Robotics-and-AI/collaborative-tasks-benchmark/stl_files/Snap/Building_Snap_Top.stl

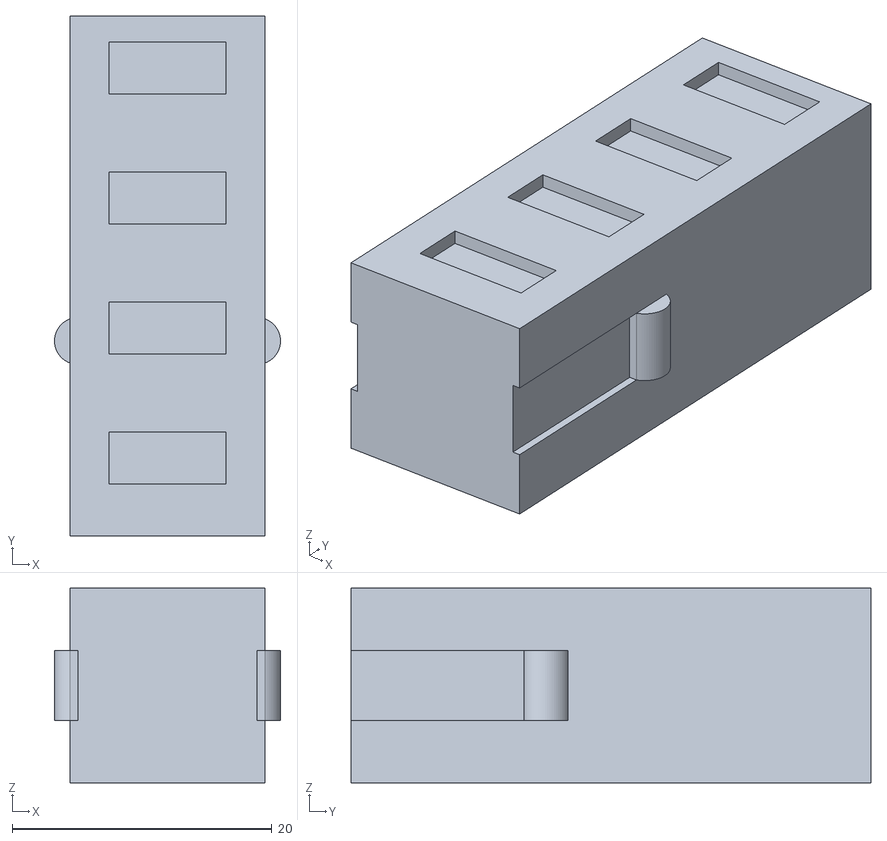
[picture p21: CAD file, 2023-07-17]
stl_files/Snap/Building_Snap_Top.stl
17.4 x 40.0 x 15.0
