Robotics-and-AI/collaborative-tasks-benchmark/stl_files/Wheel/Wheel_Base.stl

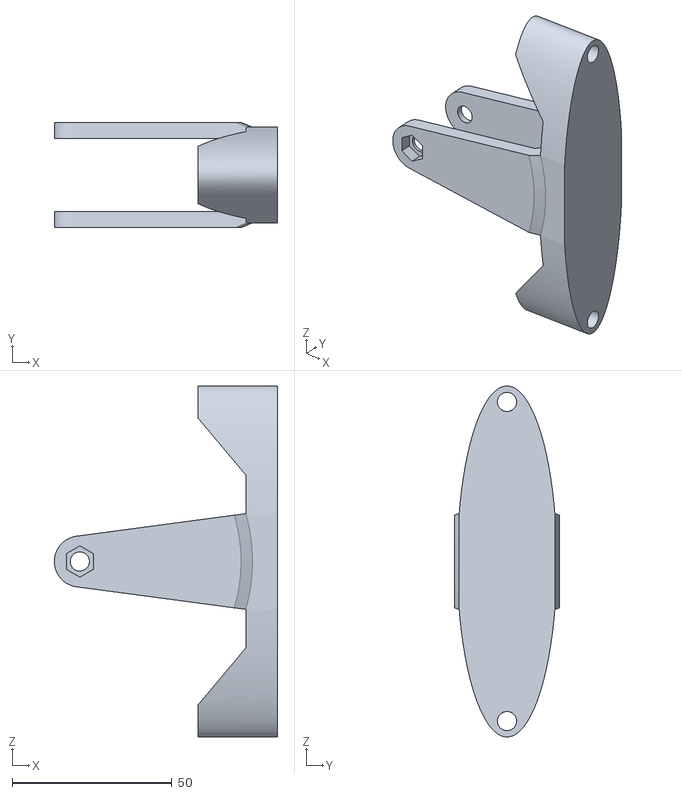
[picture p22: CAD file, 2023-09-15]
stl_files/Wheel/Wheel_Base.stl
70.0 x 33.0 x 110.0
