Robotics-and-AI/collaborative-tasks-benchmark/stl_files/Bridge/Bridge_Roof.stl

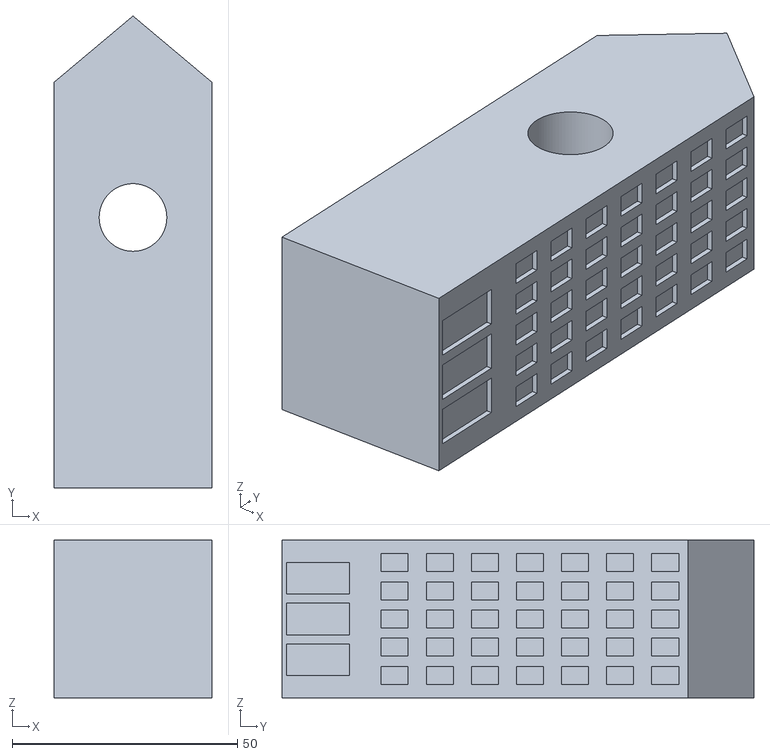
[picture p23: CAD file, 2023-07-07]
stl_files/Bridge/Bridge_Roof.stl
35.0 x 104.7 x 35.0
