Robotics-and-AI/collaborative-tasks-benchmark/stl_files/Hospital/Hospital_Top.stl

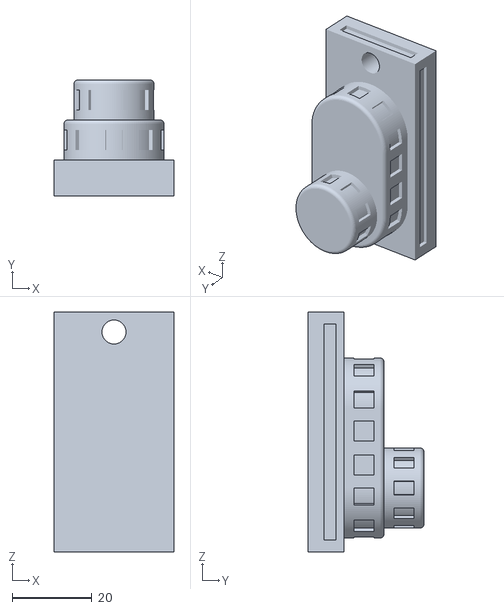
[picture p24: CAD file, 2023-07-07]
stl_files/Hospital/Hospital_Top.stl
30.0 x 29.0 x 60.0
