Robotics-and-AI/collaborative-tasks-benchmark/stl_files/Snap/Building_Snap_Lower.stl

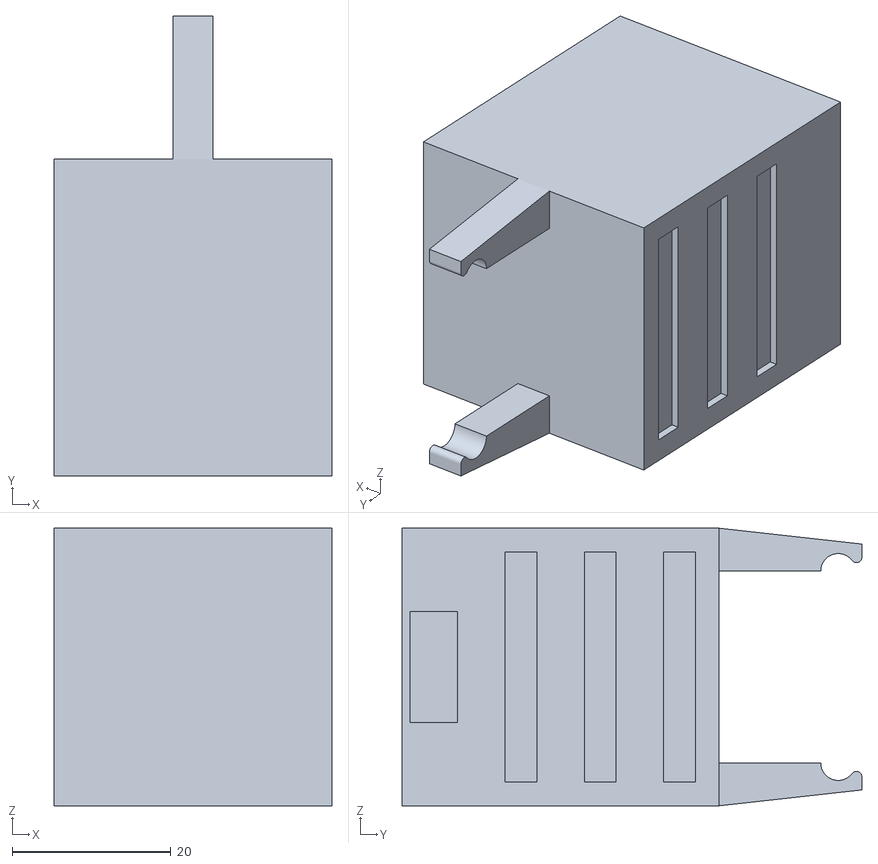
[picture p25: CAD file, 2023-07-07]
stl_files/Snap/Building_Snap_Lower.stl
35.0 x 58.0 x 35.0
